antarthureau/suuret_muinaiset/src/teensy_codebase/RTC_setup_code/RTC_setup_code.ino

#include "RTClib.h"

RTC_DS3231 rtc;
int nowSec;
int prevSec;
char daysOfTheWeek[7][12] = {"Sunday", "Monday", "Tuesday", "Wednesday", "Thursday", "Friday", "Saturday"};

void setup () {
  Serial.begin(9600);

  #ifndef ESP8266
    while (!Serial); // wait for serial port to connect. Needed for native USB
  #endif

  if (! rtc.begin()) {
    Serial.println("Couldn't find RTC");
    Serial.flush();
    while (1) delay(10);
  }

  //uncomment next line to adjust the RTC using system time during setup
  //rtc.adjust(DateTime(F(__DATE__), F(__TIME__)));

  if (rtc.lostPower()) {
    Serial.println("RTC lost power, let's set the time!");
    rtc.adjust(DateTime(F(__DATE__), F(__TIME__)));
  }

  nowSec = rtc.now().second();
  prevSec = nowSec;
}

void loop () {
  DateTime now = rtc.now();
  nowSec = now.second();

  while (nowSec != prevSec){
    Serial.print(now.year(), DEC);
    Serial.print('/');
    Serial.print(now.month(), DEC);
    Serial.print('/');
    Serial.print(now.day(), DEC);
    Serial.print(" (");
    Serial.print(daysOfTheWeek[now.dayOfTheWeek()]);
    Serial.print(") ");
    Serial.print(now.hour(), DEC);
    Serial.print(':');
    Serial.print(now.minute(), DEC);
    Serial.print(':');
    Serial.print(now.second(), DEC);
    Serial.println();
    prevSec = nowSec;
  }
}
